zenitheesc/Alcantara/hardware/kicad/shapes3D/RGB_LED_Vertical_Zenith_Short v2.step

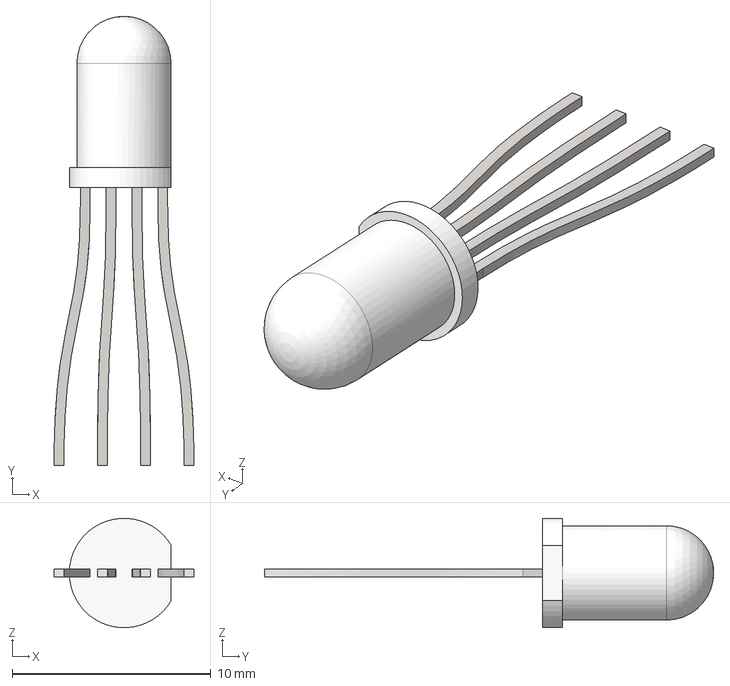
[picture p26: CAD file, 2022-01-20]
hardware/kicad/shapes3D/RGB_LED_Vertical_Zenith_Short v2.step
7.04 x 22.6 x 5.49 mm
