zenitheesc/Alcantara/hardware/kicad/shapes3D/R_0805_2012Metric.step

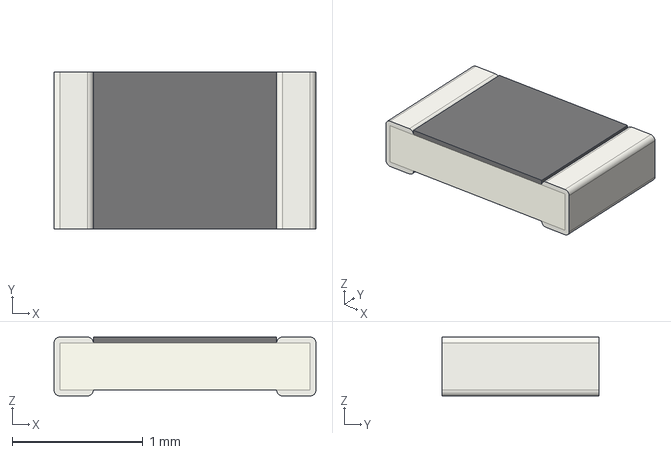
[picture p27: CAD file, 2022-01-20]
hardware/kicad/shapes3D/R_0805_2012Metric.step
2.00 x 1.20 x 0.45 mm
