zenitheesc/Alcantara/hardware/kicad/shapes3D/Texas_S-PVQFN-N16_EP2.7x2.7mm.step

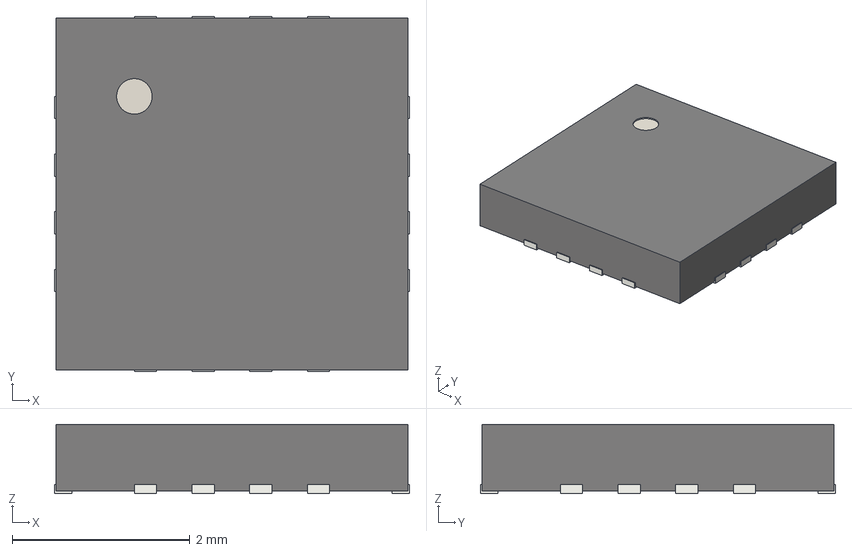
[picture p28: CAD file, 2022-01-20]
hardware/kicad/shapes3D/Texas_S-PVQFN-N16_EP2.7x2.7mm.step
4.00 x 4.00 x 0.78 mm
