zenitheesc/Alcantara/hardware/kicad/shapes3D/BTNKSC990 + Cap.step

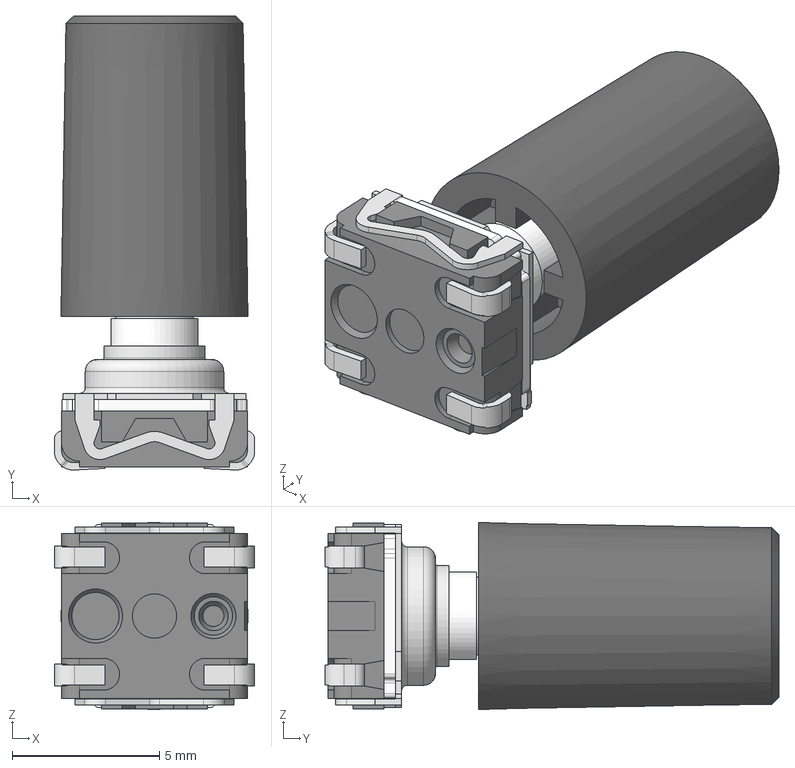
[picture p29: CAD file, 2022-01-20]
hardware/kicad/shapes3D/BTNKSC990 + Cap.step
6.80 x 15.4 x 6.35 mm
_KSC9_body
_KSC9_button
_KSC9_cover
_KSC91J_pin x 4
