zenitheesc/Alcantara/hardware/kicad/shapes3D/ESP32_Wroom.step

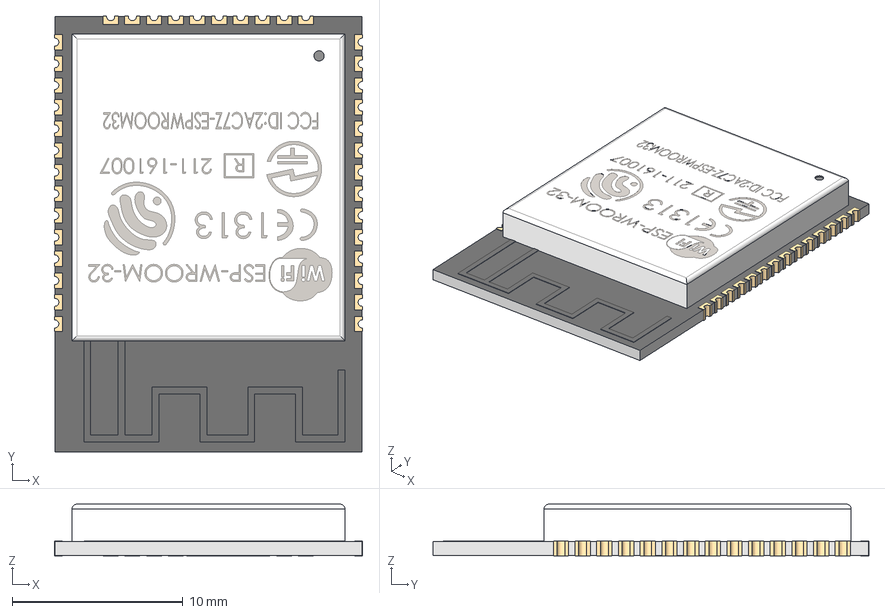
[picture p30: CAD file, 2022-01-20]
hardware/kicad/shapes3D/ESP32_Wroom.step
18.1 x 25.5 x 3.04 mm
