zenitheesc/Alcantara/hardware/kicad/shapes3D/E22-900M30S v3.step

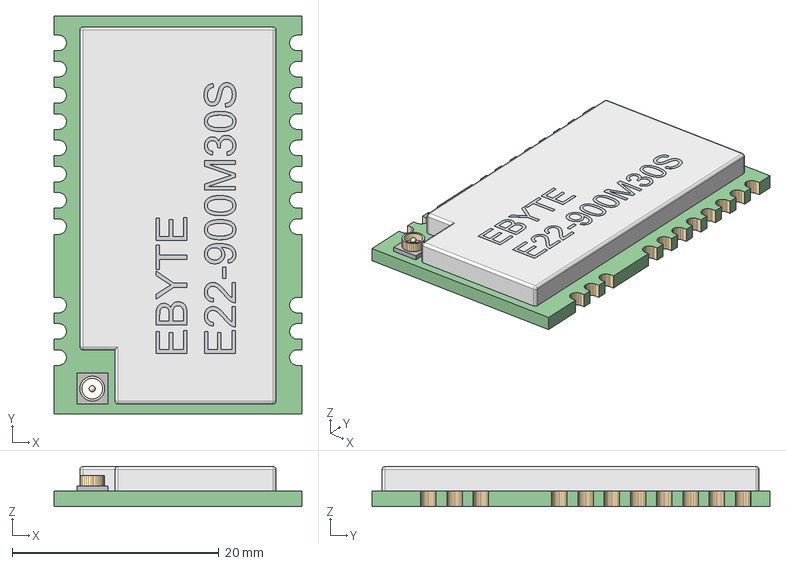
[picture p31: CAD file, 2022-01-20]
hardware/kicad/shapes3D/E22-900M30S v3.step
24.0 x 38.5 x 3.88 mm
