zenitheesc/Alcantara/hardware/kicad/shapes3D/C_0603_1608Metric.step

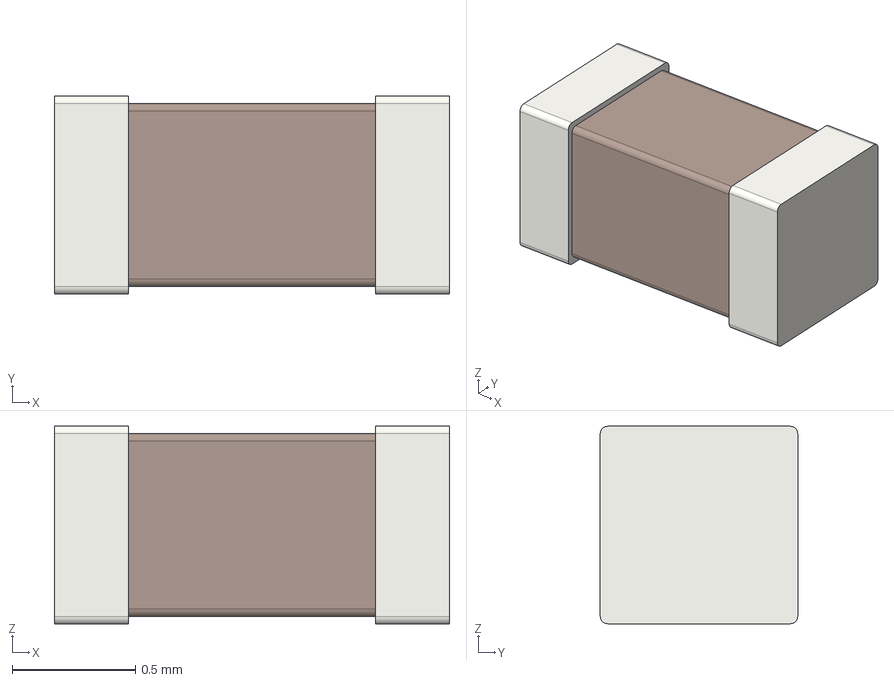
[picture p32: CAD file, 2022-01-20]
hardware/kicad/shapes3D/C_0603_1608Metric.step
1.60 x 0.8 x 0.8 mm
