zenitheesc/Alcantara/hardware/kicad/shapes3D/L_0402_1005Metric.step

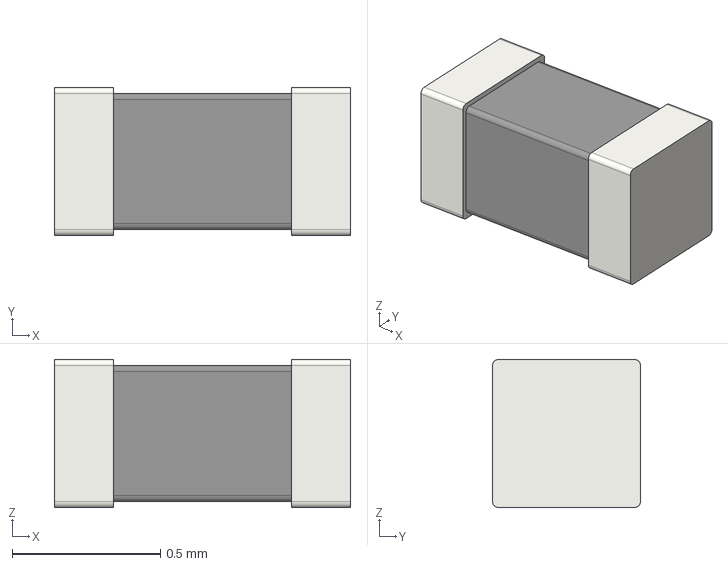
[picture p33: CAD file, 2022-01-20]
hardware/kicad/shapes3D/L_0402_1005Metric.step
1.00 x 0.5 x 0.5 mm
