zenitheesc/Alcantara/hardware/kicad/shapes3D/CUI_DEVICES_MSS-102545-14A-V-SMT.step

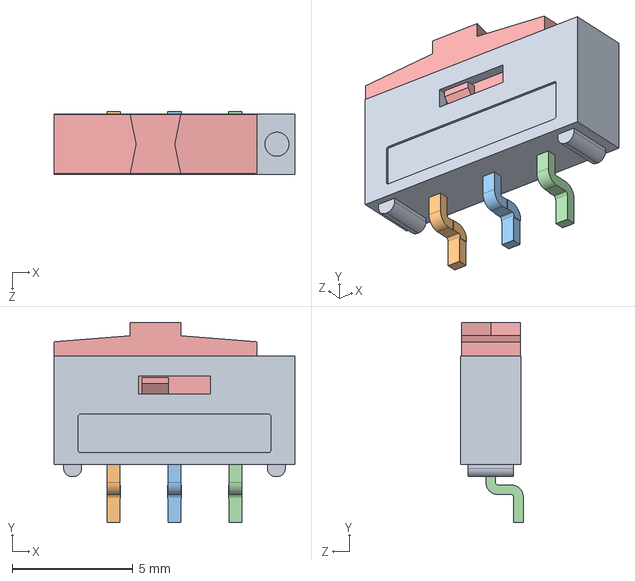
[picture p34: CAD file, 2022-01-20]
hardware/kicad/shapes3D/CUI_DEVICES_MSS-102545-14A-V-SMT.step
10.0 x 8.30 x 2.60 mm
