zenitheesc/Alcantara/hardware/kicad/shapes3D/USB_Micro-B_Molex_47346-0001.step

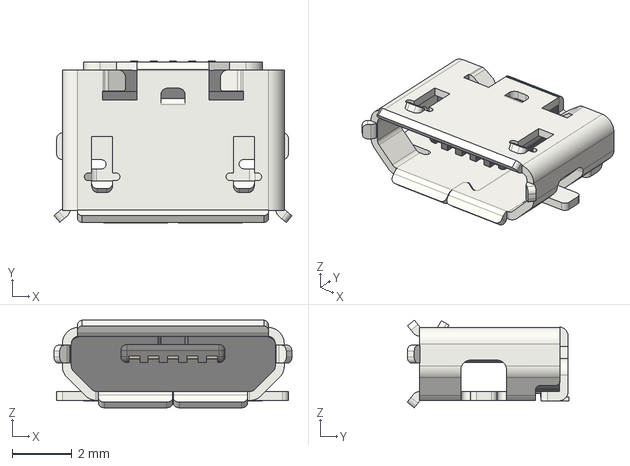
[picture p35: CAD file, 2022-01-20]
hardware/kicad/shapes3D/USB_Micro-B_Molex_47346-0001.step
7.98 x 5.42 x 2.94 mm
