zenitheesc/Alcantara/hardware/kicad/shapes3D/2N7002NXAKR.stp

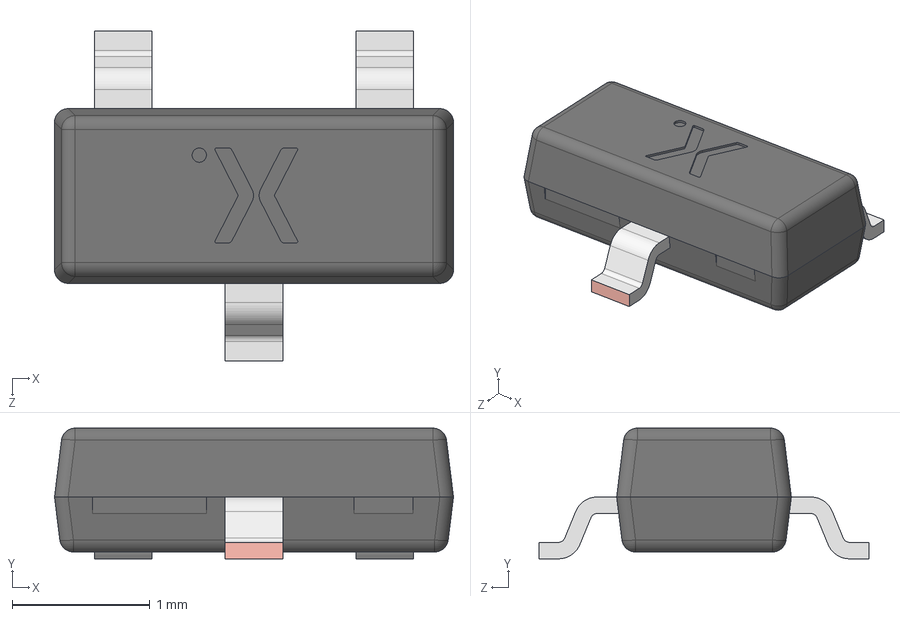
[picture p36: CAD file, 2022-01-20]
hardware/kicad/shapes3D/2N7002NXAKR.stp
2.90 x 0.95 x 2.40 mm
SOT23 lower body
SOT23 Lead x 3
SOT23 Upper body
