zenitheesc/Alcantara/hardware/kicad/shapes3D/Picoblade_5_Pin_Horizontal v2.step

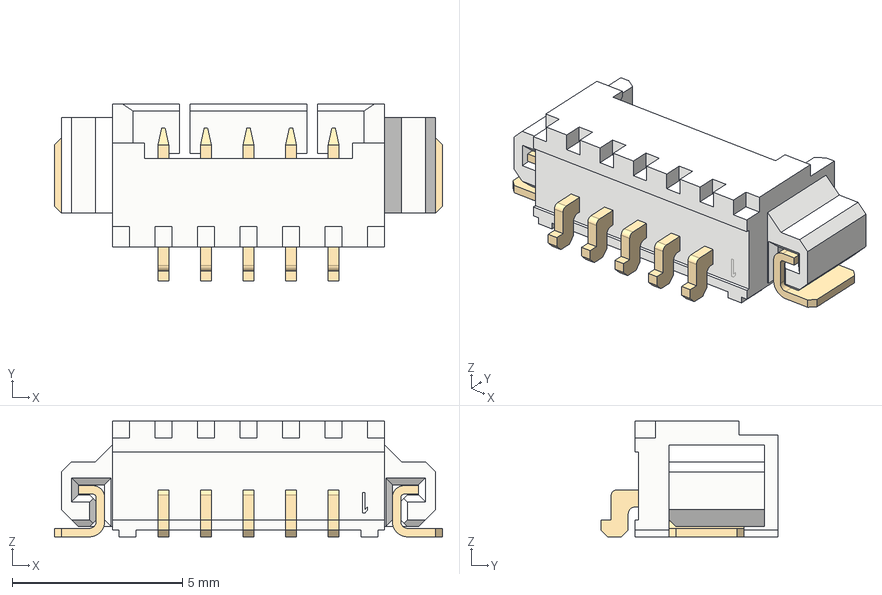
[picture p37: CAD file, 2022-01-20]
hardware/kicad/shapes3D/Picoblade_5_Pin_Horizontal v2.step
11.4 x 5.20 x 3.40 mm
