zenitheesc/Alcantara/hardware/kicad/shapes3D/BatteryHolder_Keystone_1042_1x18650_No_Stubs.step

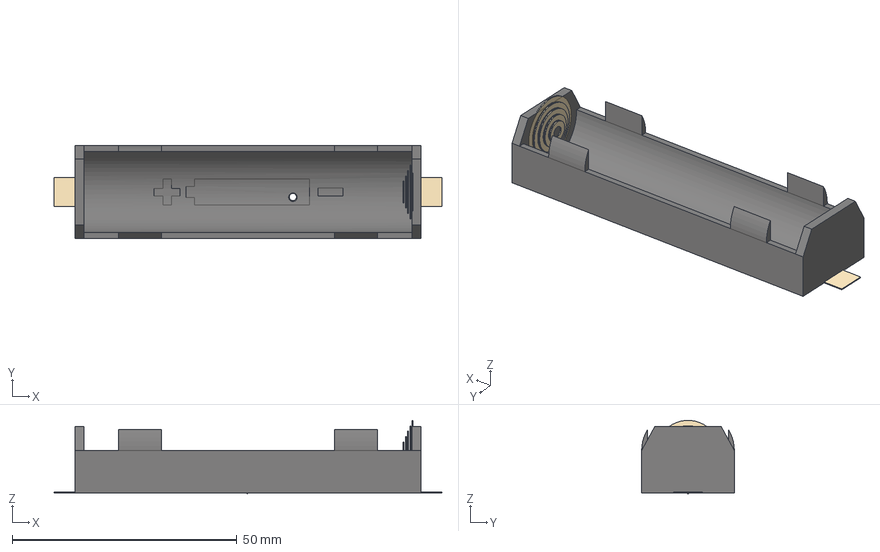
[picture p38: CAD file, 2022-01-20]
hardware/kicad/shapes3D/BatteryHolder_Keystone_1042_1x18650_No_Stubs.step
86.4 x 20.6 x 16.3 mm
