zenitheesc/Alcantara/hardware/kicad/shapes3D/D_0603_1608Metric.step

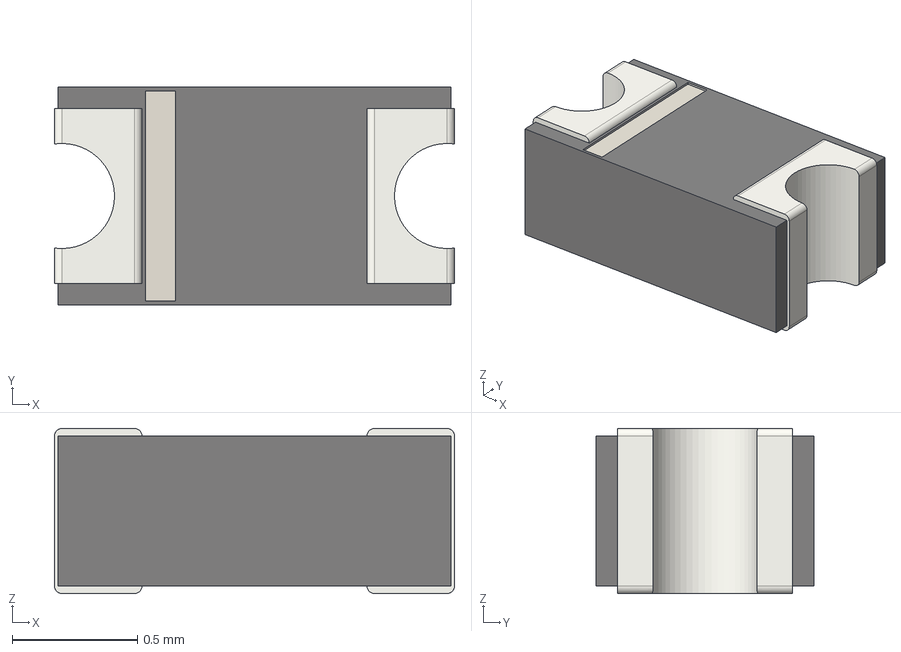
[picture p39: CAD file, 2022-01-20]
hardware/kicad/shapes3D/D_0603_1608Metric.step
1.60 x 0.87 x 0.66 mm
