zenitheesc/Alcantara/hardware/kicad/shapes3D/Amphenol 132415.step

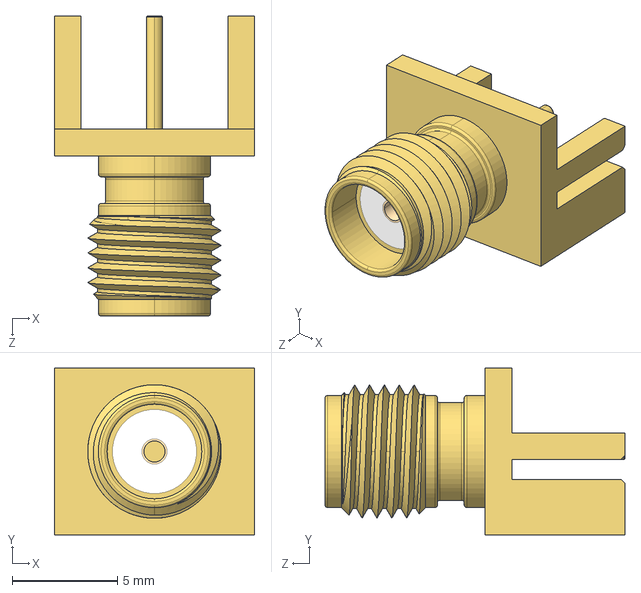
[picture p40: CAD file, 2022-01-20]
hardware/kicad/shapes3D/Amphenol 132415.step
9.52 x 7.92 x 14.3 mm
