zenitheesc/Alcantara/hardware/kicad/shapes3D/AST0760MCTRQ.step

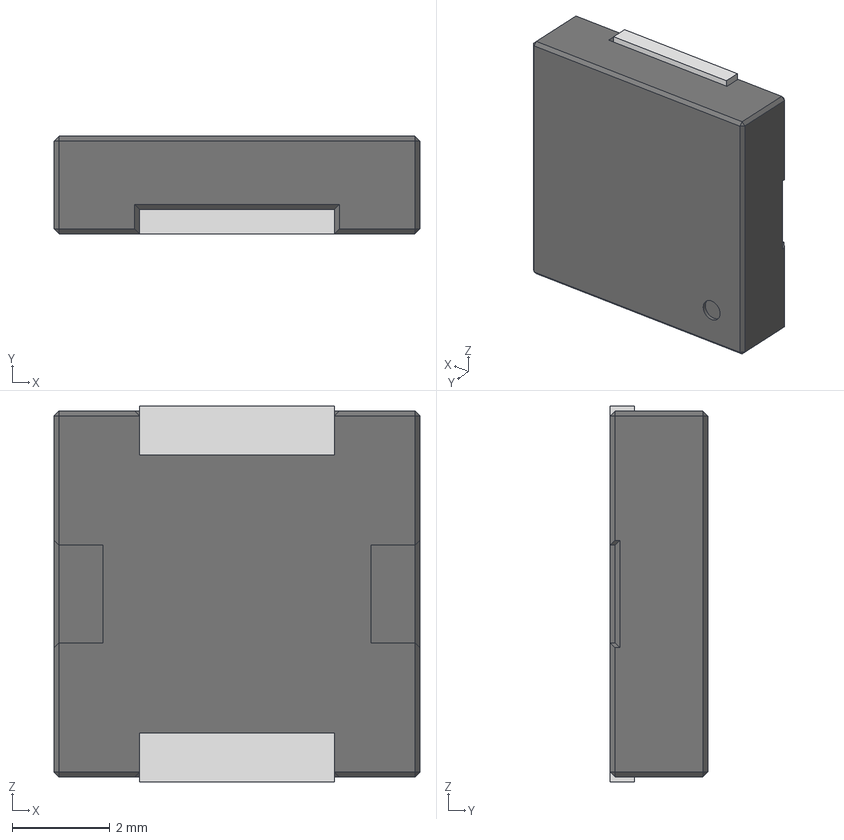
[picture p41: CAD file, 2022-01-20]
hardware/kicad/shapes3D/AST0760MCTRQ.step
7.50 x 2.00 x 7.70 mm
