zenitheesc/Alcantara/hardware/kicad/shapes3D/SOT-23-6.step

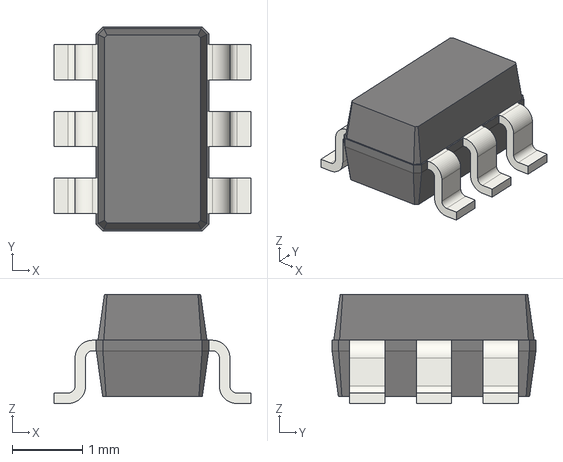
[picture p42: CAD file, 2022-01-20]
hardware/kicad/shapes3D/SOT-23-6.step
2.80 x 2.90 x 1.55 mm
