zenitheesc/Alcantara/hardware/kicad/shapes3D/EVPAA.step

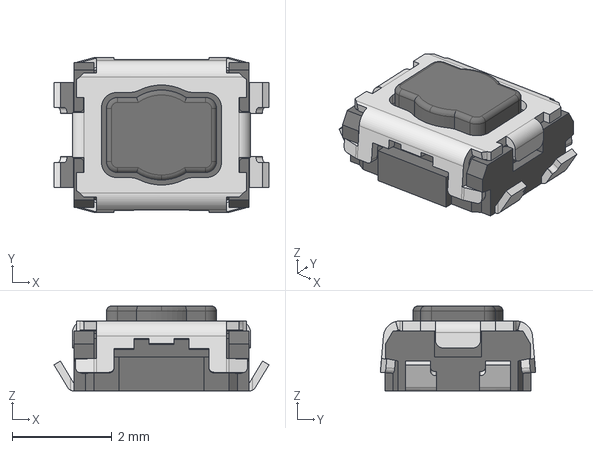
[picture p43: CAD file, 2022-01-20]
hardware/kicad/shapes3D/EVPAA.step
4.30 x 3.11 x 1.70 mm
