zenitheesc/Alcantara/hardware/kicad/shapes3D/C_1206_3216Metric.step

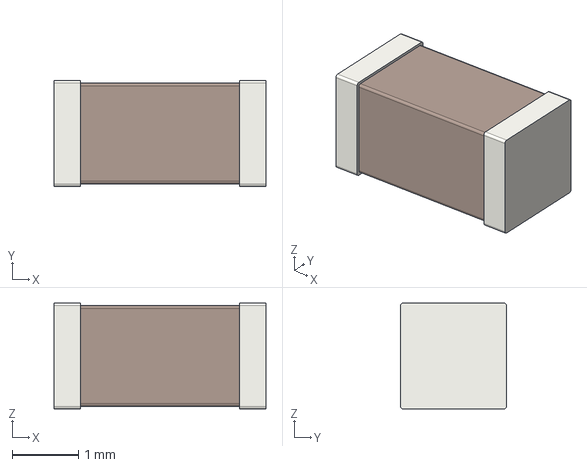
[picture p44: CAD file, 2022-01-20]
hardware/kicad/shapes3D/C_1206_3216Metric.step
3.20 x 1.60 x 1.60 mm
