zenitheesc/Alcantara/hardware/kicad/shapes3D/User Library-neo-m8n.step

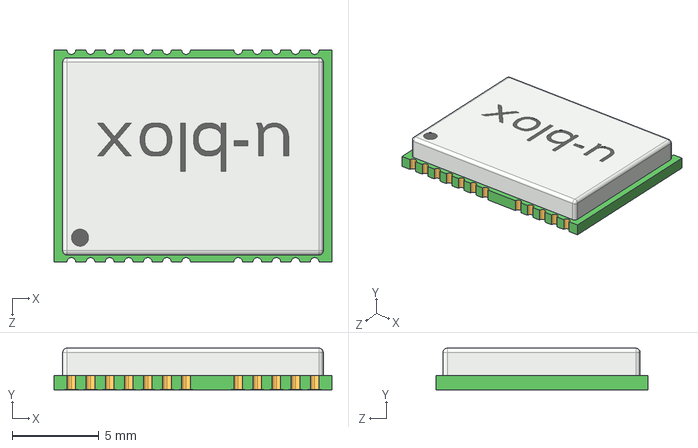
[picture p45: CAD file, 2022-01-20]
hardware/kicad/shapes3D/User Library-neo-m8n.step
16.0 x 2.40 x 12.2 mm
