zenitheesc/Alcantara/hardware/kicad/shapes3D/PJS008U-3000-0.stp

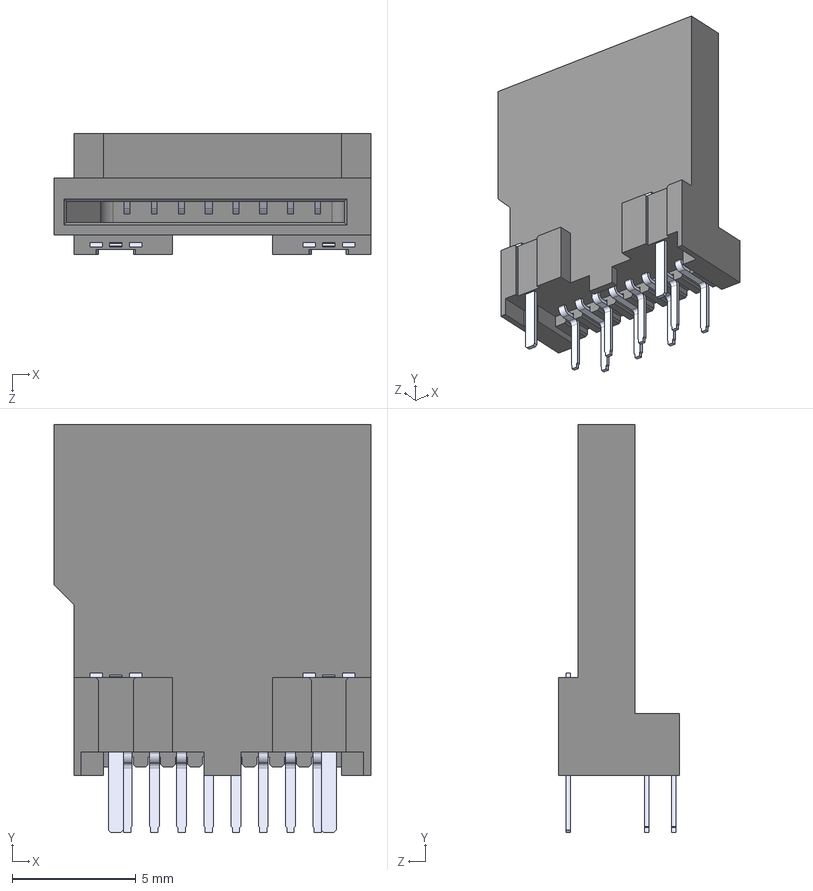
[picture p46: CAD file, 2022-01-20]
hardware/kicad/shapes3D/PJS008U-3000-0.stp
12.8 x 16.5 x 4.90 mm
