zenitheesc/Alcantara/hardware/kicad/shapes3D/SOT-223.step

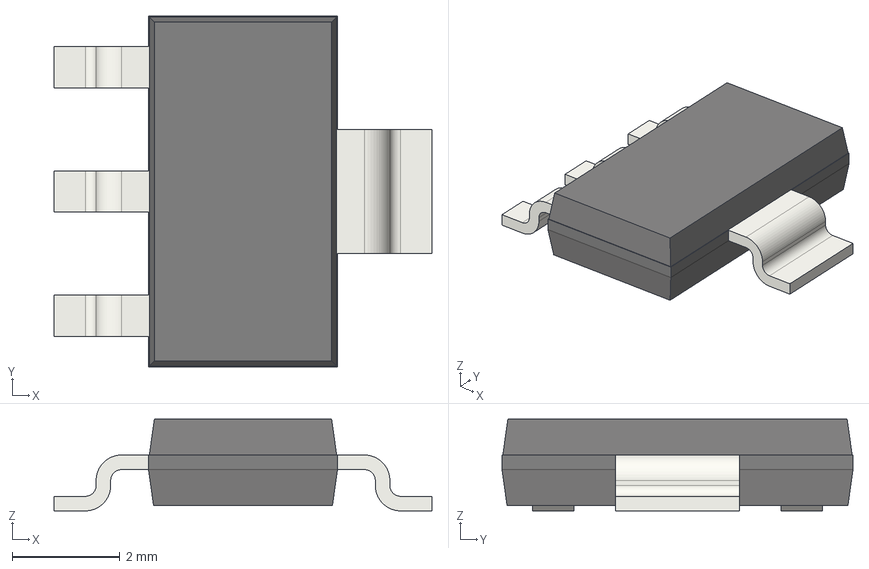
[picture p47: CAD file, 2022-01-20]
hardware/kicad/shapes3D/SOT-223.step
7.00 x 6.50 x 1.70 mm
