zenitheesc/Alcantara/hardware/kicad/shapes3D/TLV809ED29DBZR.stp

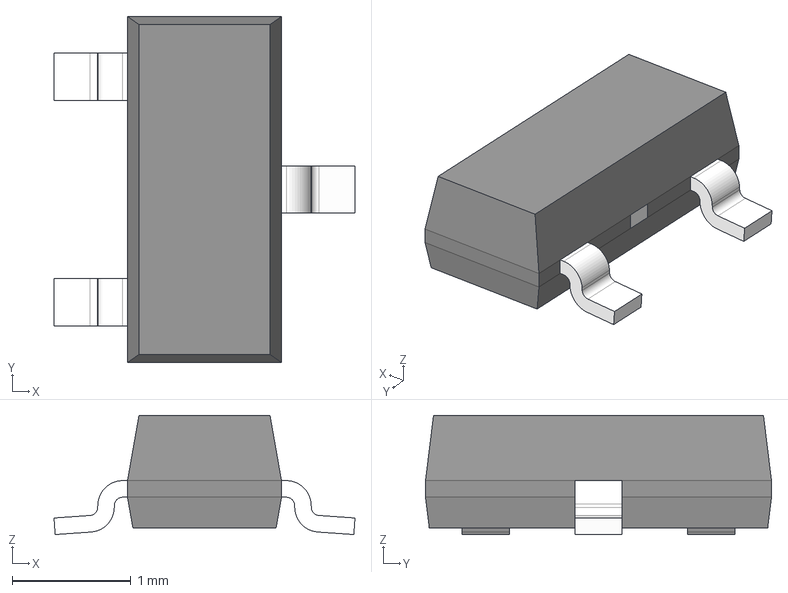
[picture p48: CAD file, 2022-01-20]
hardware/kicad/shapes3D/TLV809ED29DBZR.stp
2.54 x 2.92 x 1.01 mm
BODY-SOT
LEAD-SOT x 3
PIN1-ID
TIEBAR
