zenitheesc/Alcantara/hardware/kicad/shapes3D/CP_Elec_5x5.3.step

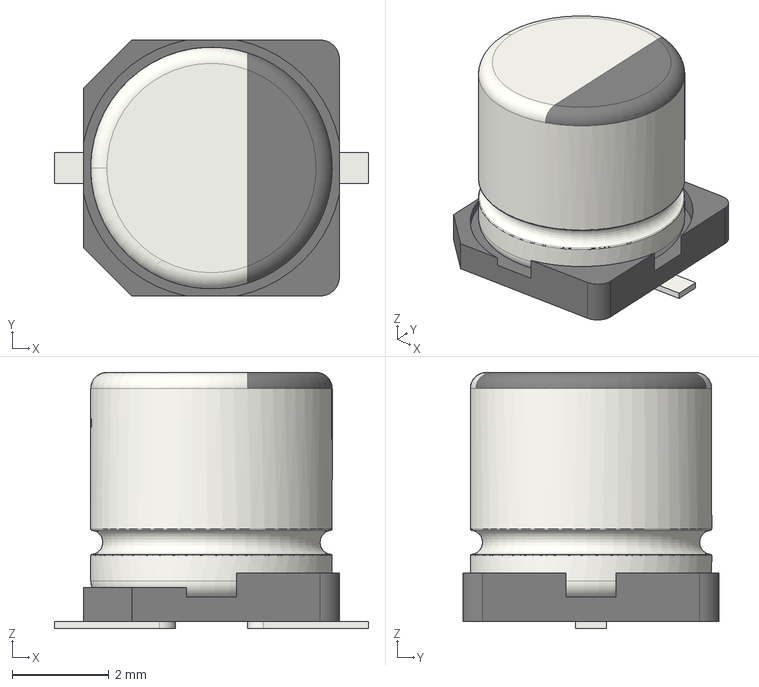
[picture p49: CAD file, 2022-01-20]
hardware/kicad/shapes3D/CP_Elec_5x5.3.step
6.50 x 5.30 x 5.30 mm
